saschadaemgen/halo-gauge-experiment/hardware/jig/jig_v6_frame.stl

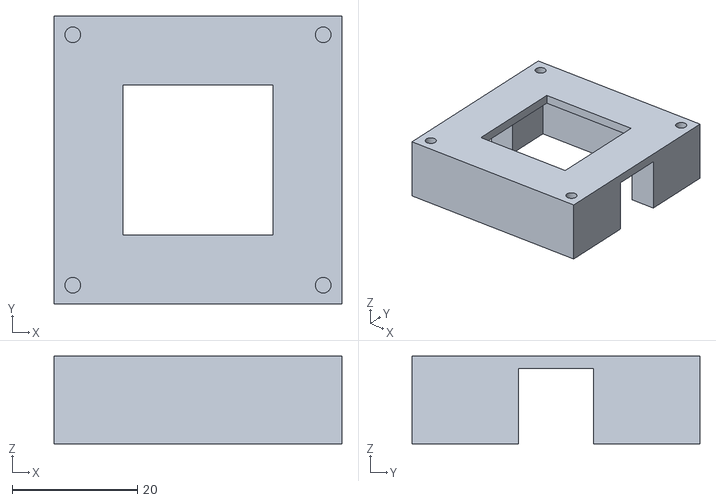
[picture p35: CAD file, 2026-09-12]
hardware/jig/jig_v6_frame.stl
46.0 x 46.0 x 14.0
