saschadaemgen/halo-gauge-experiment/hardware/jig/jig_v6_carrier.stl

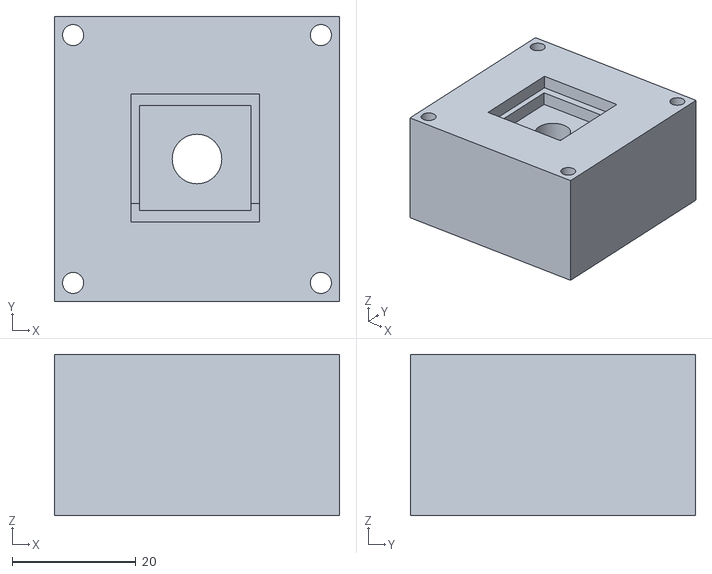
[picture p36: CAD file, 2026-09-12]
hardware/jig/jig_v6_carrier.stl
46.0 x 46.0 x 26.0
